ZeshuLiu/PolaMiya/结构Rev2/电路/机身主控/C_0603_1608Metric.SLDASM

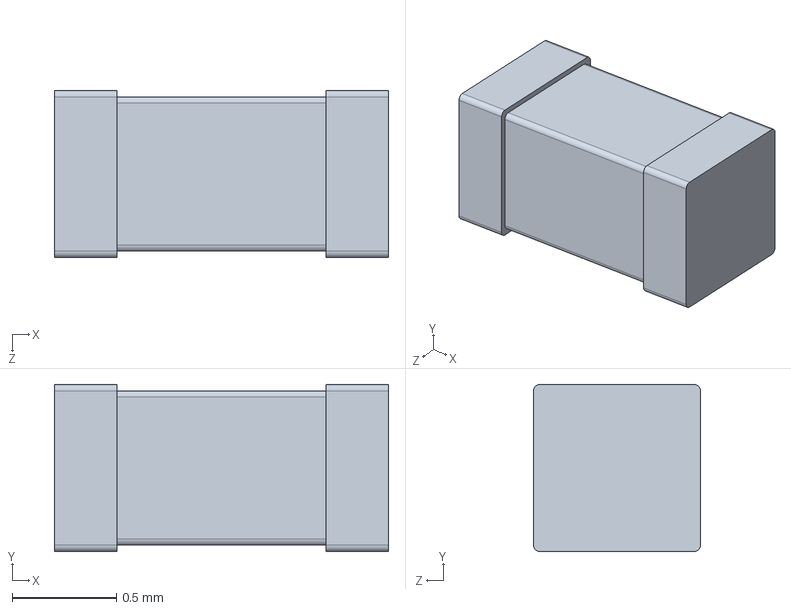
[picture p11: CAD file, 2025-02-23, last stored version]
结构Rev2/电路/机身主控/C_0603_1608Metric.SLDASM
1.60 x 0.8 x 0.8 mm
