ZeshuLiu/PolaMiya/电路/sdm18串口.SLDPRT

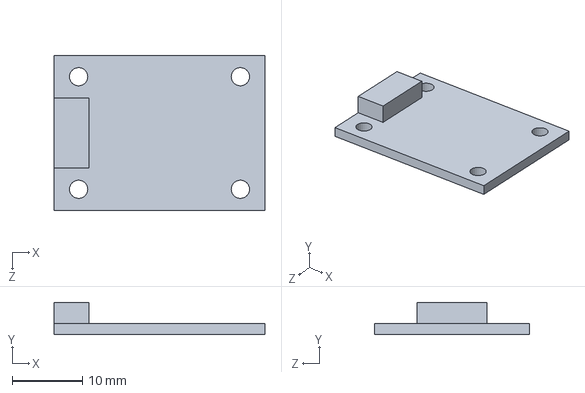
[picture p12: CAD file, 2025-06-10, last stored version]
电路/sdm18串口.SLDPRT
30.0 x 4.60 x 22.0 mm
