ZeshuLiu/PolaMiya/电路/主控器/DispKey/DispKeyR1_0.step

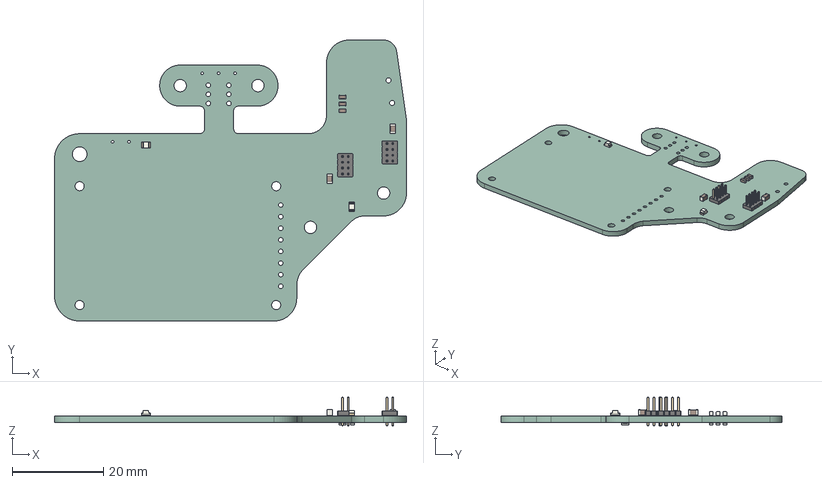
[picture p13: CAD file, 2025-06-10, last stored version]
电路/主控器/DispKey/DispKeyR1_0.step
77.0 x 61.5 x 6.30 mm
LED_0805_2012Metric x 2
C_0805_2012Metric x 2
C_0603_1608Metric x 3
PinHeader_2x04_P1.27mm_Vertical x 2
R_0603_1608Metric x 4
DispKey_PCB
