ZeshuLiu/PolaMiya/结构/原厂零件/吐片口机身钣金.SLDPRT

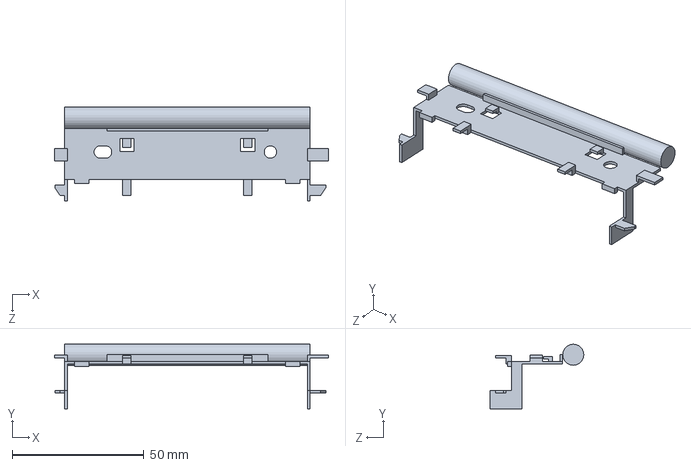
[picture p16: CAD file, 2025-02-23, last stored version]
结构/原厂零件/吐片口机身钣金.SLDPRT
103.8 x 24.5 x 35.5 mm
