ZeshuLiu/PolaMiya/结构/吐片机构/齿轮罩.SLDPRT

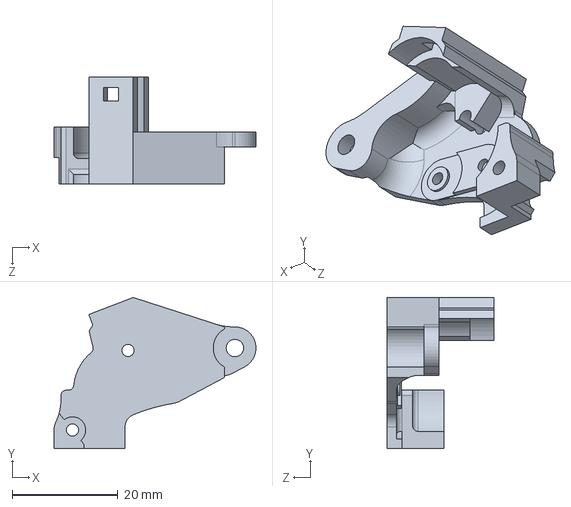
[picture p17: CAD file, 2025-07-19, last stored version]
结构/吐片机构/齿轮罩.SLDPRT
38.2 x 28.6 x 20.2 mm
