ZeshuLiu/PolaMiya/结构/外壳/STL/6吐片上巴.STL

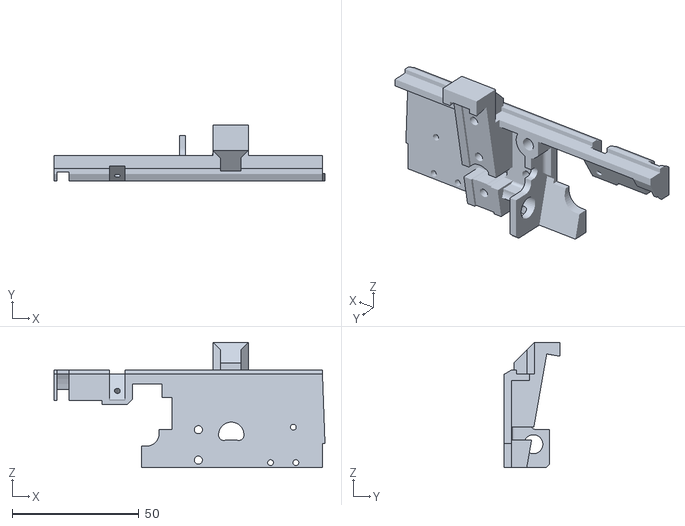
[picture p18: CAD file, 2025-02-23, last stored version]
结构/外壳/STL/6吐片上巴.STL
107.0 x 22.0 x 49.5
