ZeshuLiu/PolaMiya/结构/外壳/后挡板.SLDPRT

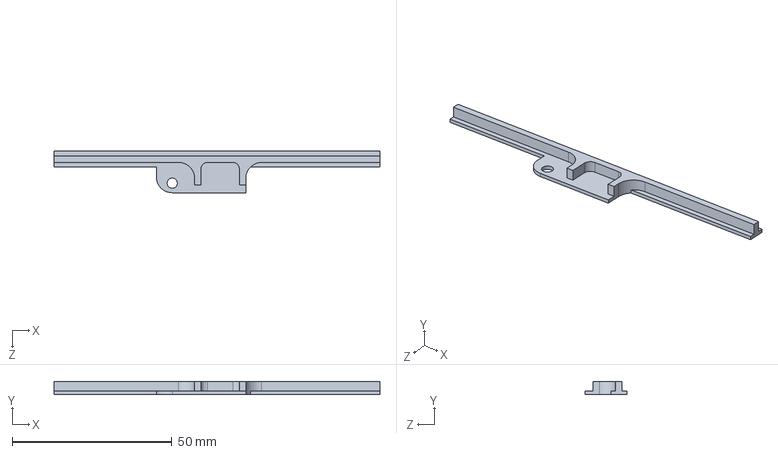
[picture p19: CAD file, 2025-09-27, last stored version]
结构/外壳/后挡板.SLDPRT
102.0 x 4.00 x 13.0 mm
