ZeshuLiu/PolaMiya/结构/片仓/STL/15左侧副支架.3mf

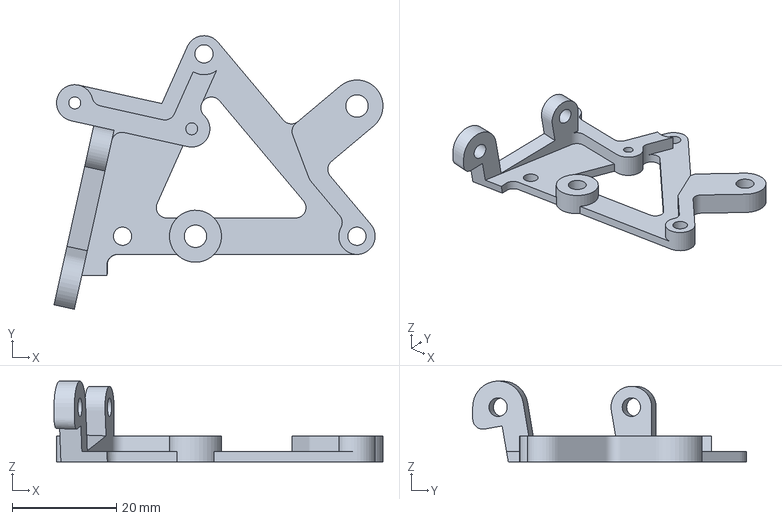
[picture p20: CAD file, 2025-06-10, last stored version]
结构/片仓/STL/15左侧副支架.3mf
63.2 x 52.5 x 15.5 mm
