ZeshuLiu/PolaMiya/结构/配件/STL/片仓消光绒.3mf

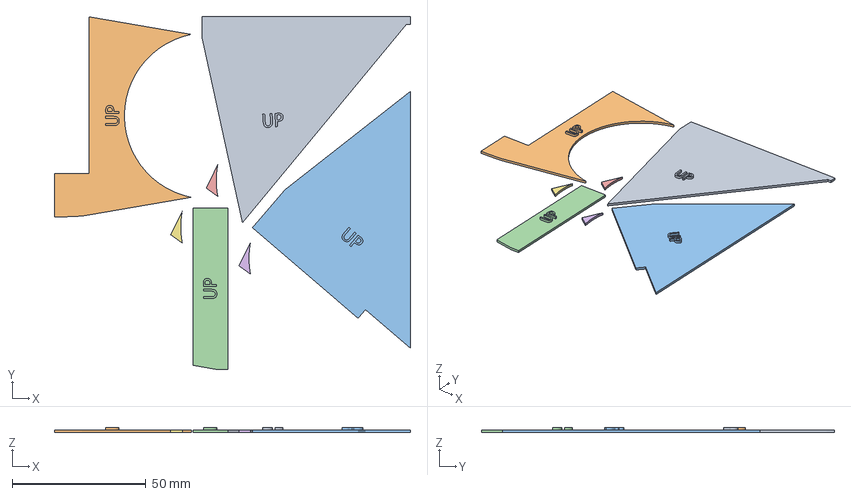
[picture p21: CAD file, 2025-09-27, last stored version]
结构/配件/STL/片仓消光绒.3mf
133.1 x 131.8 x 2.00 mm
片仓消光绒2.STL
片仓消光绒3.STL
片仓消光绒1.STL
片仓消光绒5.STL
片仓消光绒4.STL x 3
