ZeshuLiu/PolaMiya/结构/配件/片仓消光绒6.SLDPRT

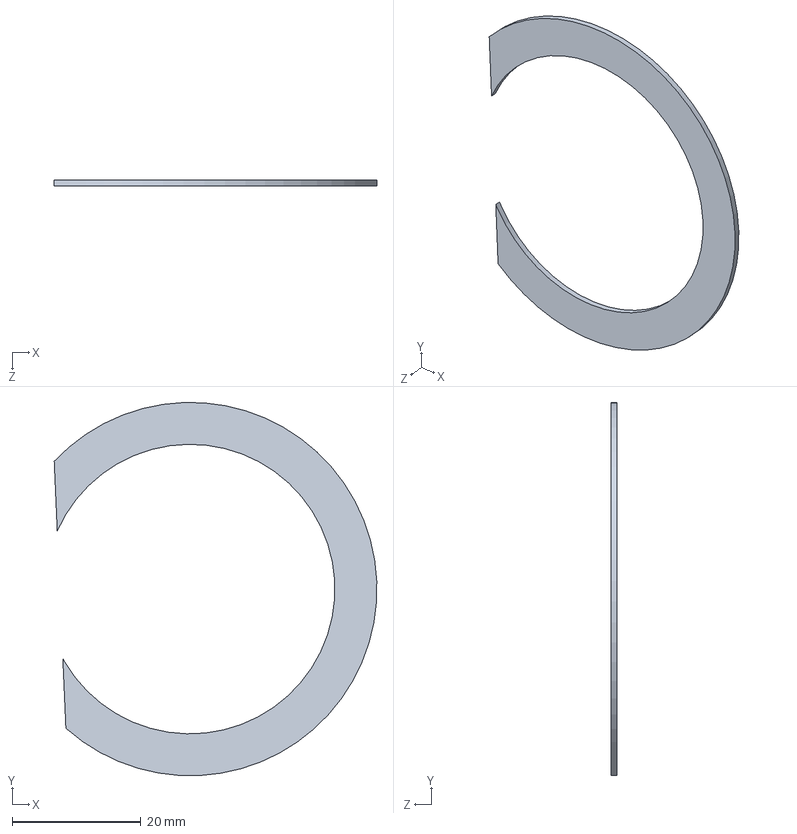
[picture p22: CAD file, 2025-09-27, last stored version]
结构/配件/片仓消光绒6.SLDPRT
50.1 x 58.0 x 1.00 mm
