ZeshuLiu/PolaMiya/结构Rev2/t/PolamiaPCB.step

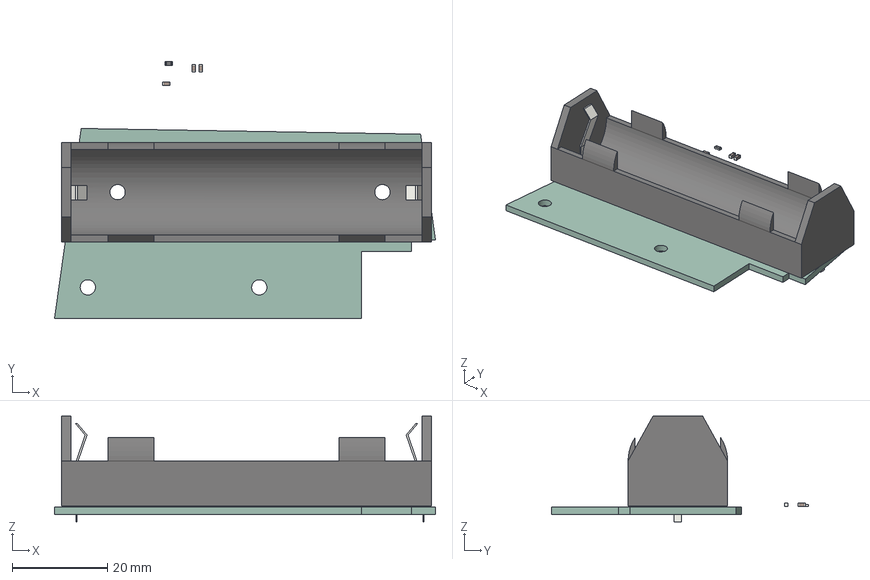
[picture p23: CAD file, 2025-02-23, last stored version]
结构Rev2/t/PolamiaPCB.step
80.0 x 53.9 x 22.2 mm
C_0603_1608Metric x 3
R_0603_1608Metric
MPD_BH_18650_PC2
PolamiaPCB_PCB
