ZeshuLiu/PolaMiya/结构Rev2/吐片机构/stps/吐片机构.STEP

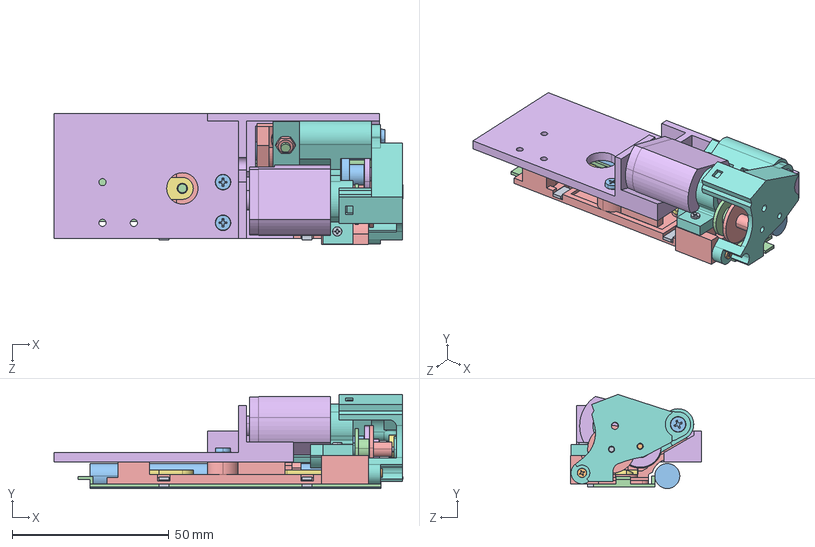
[picture p24: CAD file, 2025-02-23, last stored version]
结构Rev2/吐片机构/stps/吐片机构.STEP
111.5 x 30.1 x 42.0 mm
吐片口机身钣金
吐片钣金连接件
MG825
吐片钣金固定销 x 2
马达座
1.6x14.6
1.6x20.6
齿轮A
齿轮B
齿轮C
齿轮D
齿轮E
齿轮罩
cross recessed cheese head screws type a gb_GB_CROSS_SCREWS_TYPE135 M2X7-N
cross recessed cheese head screws type a gb_GB_CROSS_SCREWS_TYPE135 M2X6-N
cross recessed cheese head screws type a gb_GB_CROSS_SCREWS_TYPE135 M3X6-N x 3
cross recessed cheese head screws type a gb_GB_CROSS_SCREWS_TYPE135 M3X8-N
hex thin nuts-grades ab-chamfered gb_GB_FASTENER_NUT_STNAB M3-N
吐片上巴
