ZeshuLiu/PolaMiya/结构Rev2/测试用/法兰距测试/对焦框10080.SLDPRT

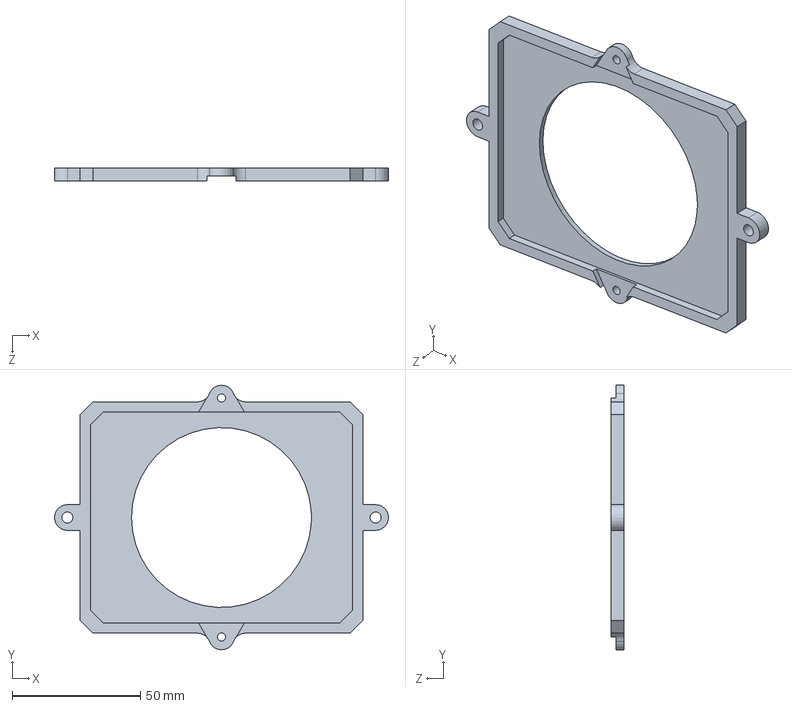
[picture p25: CAD file, 2025-02-23, last stored version]
结构Rev2/测试用/法兰距测试/对焦框10080.SLDPRT
130.0 x 103.0 x 5.00 mm
