ZeshuLiu/PolaMiya/结构Rev2/片仓吐片总成/STL/片仓吐片一体STL.3mf

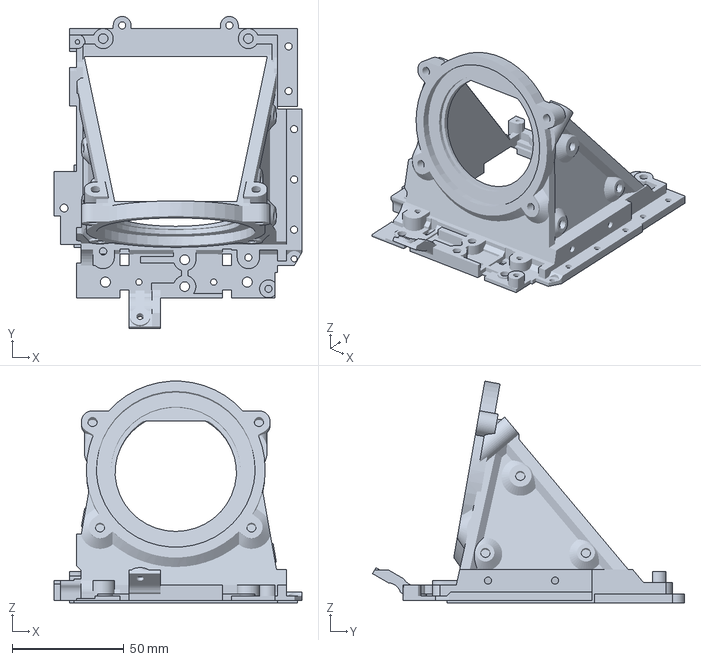
[picture p26: CAD file, 2025-09-27, last stored version]
结构Rev2/片仓吐片总成/STL/片仓吐片一体STL.3mf
111.0 x 139.6 x 99.3 mm
