ZeshuLiu/PolaMiya/结构Rev2/片仓吐片总成/吐片上巴.SLDPRT

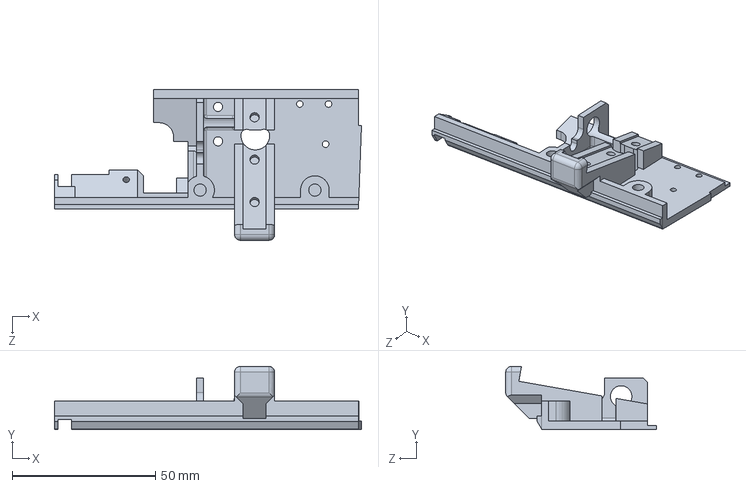
[picture p27: CAD file, 2025-09-27, last stored version]
结构Rev2/片仓吐片总成/吐片上巴.SLDPRT
107.0 x 22.0 x 52.5 mm
