ZeshuLiu/PolaMiya/结构Rev2/电路/DispKey_R1_0/DispKey_PCB.SLDPRT

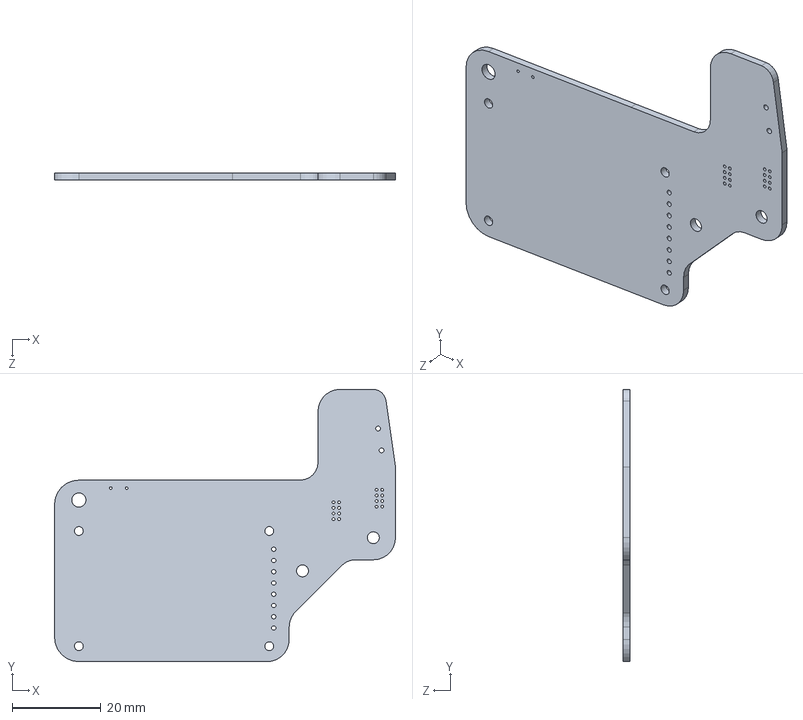
[picture p28: CAD file, 2025-06-10, last stored version]
结构Rev2/电路/DispKey_R1_0/DispKey_PCB.SLDPRT
77.0 x 61.5 x 1.51 mm
