ZeshuLiu/PolaMiya/结构Rev2/电路/电池按钮.SLDPRT

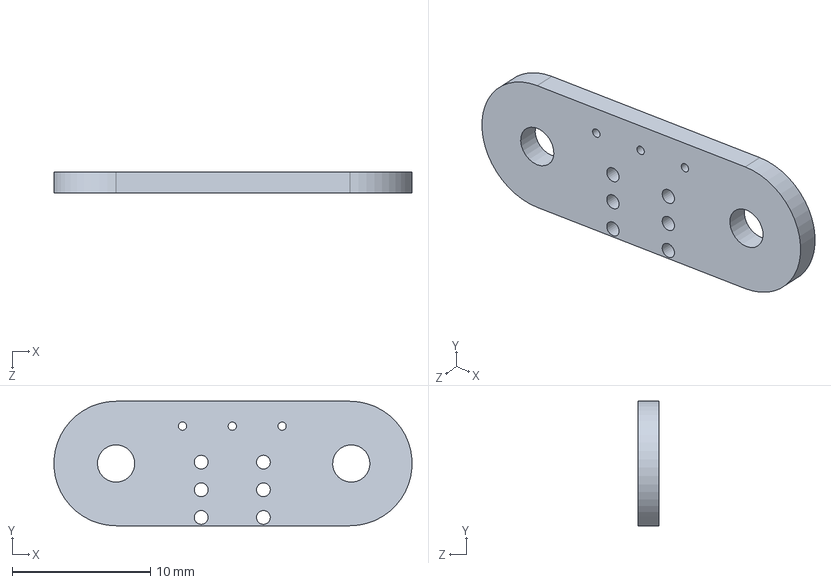
[picture p29: CAD file, 2025-06-10, last stored version]
结构Rev2/电路/电池按钮.SLDPRT
25.9 x 9.00 x 1.51 mm
