ZeshuLiu/PolaMiya/结构Rev2/配件/Mamiya127镜头盖后盖.SLDPRT

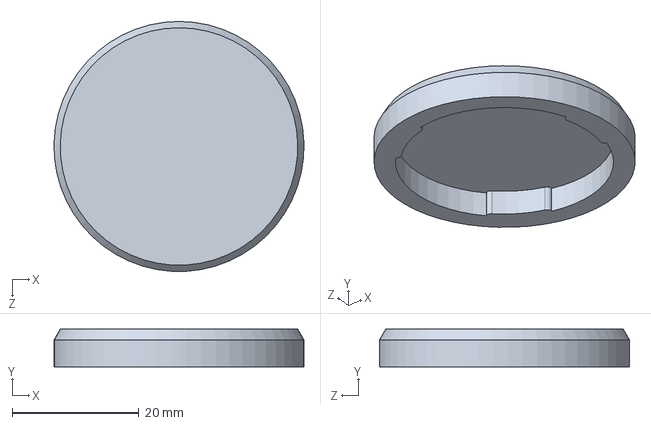
[picture p30: CAD file, 2025-02-23, last stored version]
结构Rev2/配件/Mamiya127镜头盖后盖.SLDPRT
39.5 x 6.00 x 39.5 mm
