ZeshuLiu/PolaMiya/结构Rev2/配件/STL/55mm_Spring.stl

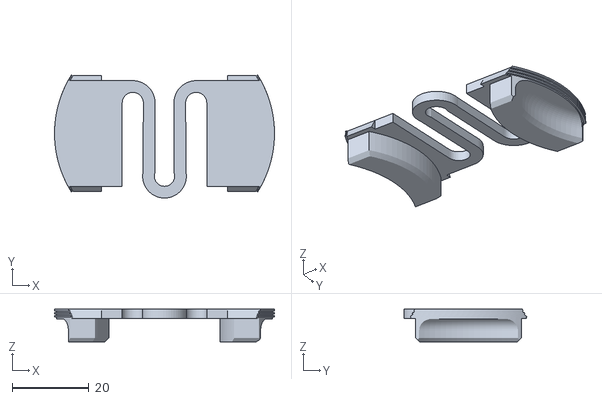
[picture p31: CAD file, 2025-02-23, last stored version]
结构Rev2/配件/STL/55mm_Spring.stl
57.2 x 32.0 x 8.50
