ZeshuLiu/PolaMiya/结构Rev2/采购零件/大头拨轮.SLDPRT

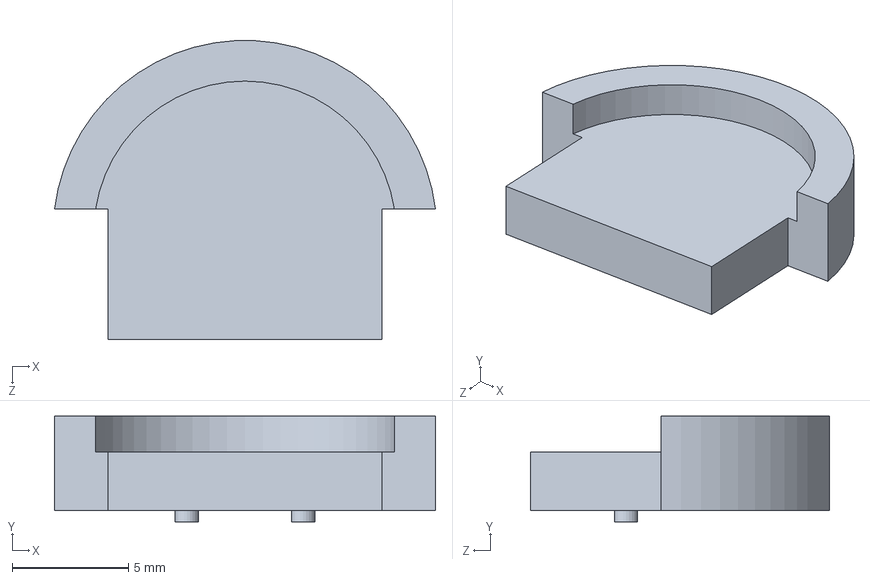
[picture p32: CAD file, 2025-06-29, last stored version]
结构Rev2/采购零件/大头拨轮.SLDPRT
16.4 x 4.55 x 12.8 mm
