ZeshuLiu/PolaMiya/结构Rev2/镜头总成/STL/1调焦桶盖+4内环.3mf

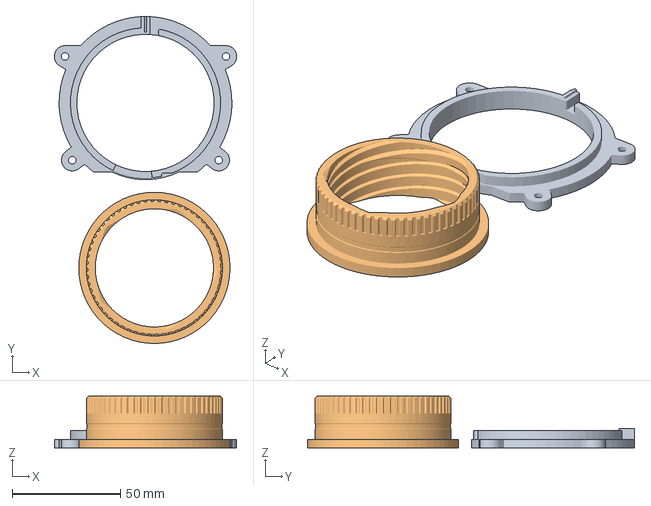
[picture p33: CAD file, 2025-02-23, last stored version]
结构Rev2/镜头总成/STL/1调焦桶盖+4内环.3mf
84.5 x 151.3 x 24.0 mm
1调焦桶盖.STL
4内环.STL
