ZeshuLiu/PolaMiya/结构Rev2N/全息取景器/标靶.SLDPRT

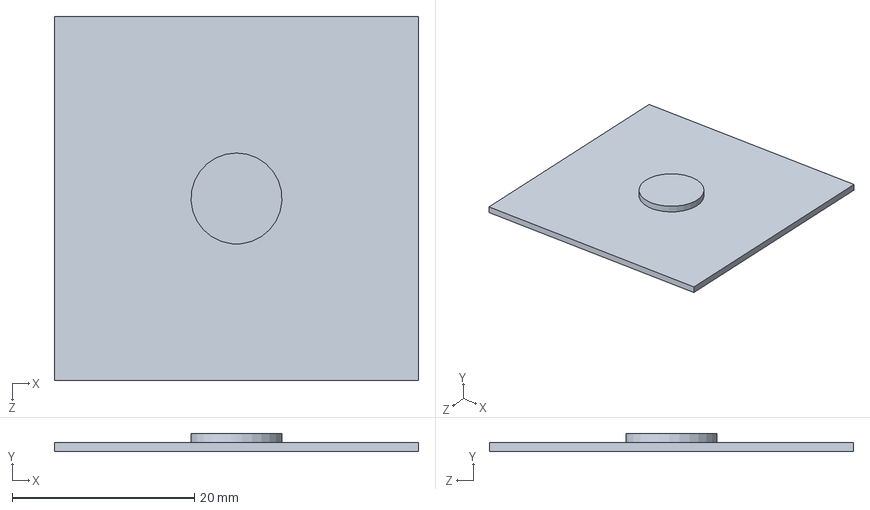
[picture p34: CAD file, 2026-03-20, last stored version]
结构Rev2N/全息取景器/标靶.SLDPRT
40.0 x 2.00 x 40.0 mm
