ZeshuLiu/PolaMiya/结构Rev2N/吐片机构/STLs/钣金突起衬垫.3mf

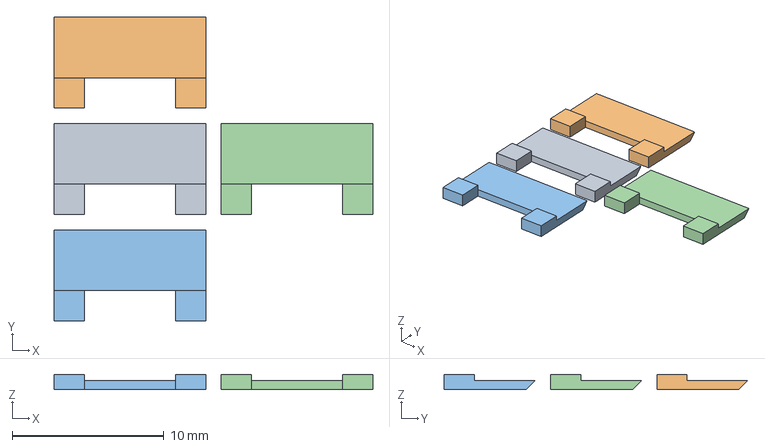
[picture p35: CAD file, 2026-02-14, last stored version]
结构Rev2N/吐片机构/STLs/钣金突起衬垫.3mf
21.0 x 20.0 x 1.00 mm
钣金突起衬垫.STL x 4
