ZeshuLiu/PolaMiya/结构Rev2N/吐片机构/stps/马达座.STEP

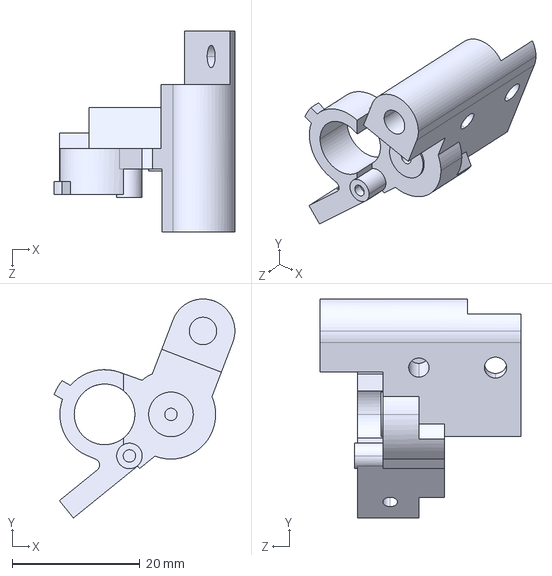
[picture p36: CAD file, 2025-02-23, last stored version]
结构Rev2N/吐片机构/stps/马达座.STEP
28.3 x 34.3 x 31.5 mm
