ZeshuLiu/PolaMiya/结构Rev2N/吐片机构/齿轮定位.SLDPRT

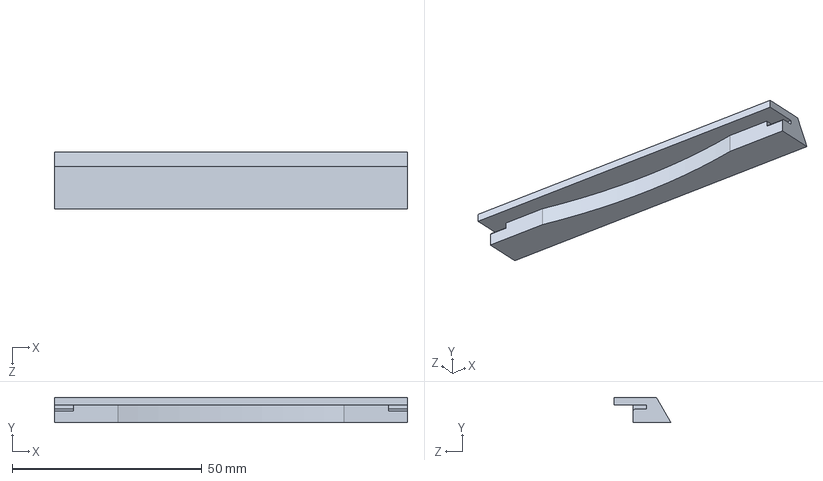
[picture p37: CAD file, 2026-02-14, last stored version]
结构Rev2N/吐片机构/齿轮定位.SLDPRT
93.1 x 6.60 x 15.0 mm
