ZeshuLiu/PolaMiya/结构Rev2N/外壳/STL/闪光灯线.3mf

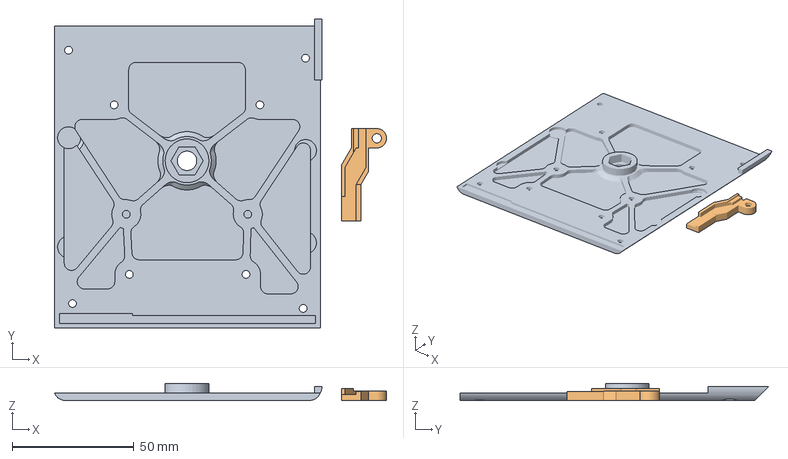
[picture p38: CAD file, 2025-09-27, last stored version]
结构Rev2N/外壳/STL/闪光灯线.3mf
136.6 x 127.0 x 7.00 mm
底壳.STL
闪光灯线.STL
