ZeshuLiu/PolaMiya/结构Rev2N/消光绒模板/STL/消光绒.3mf

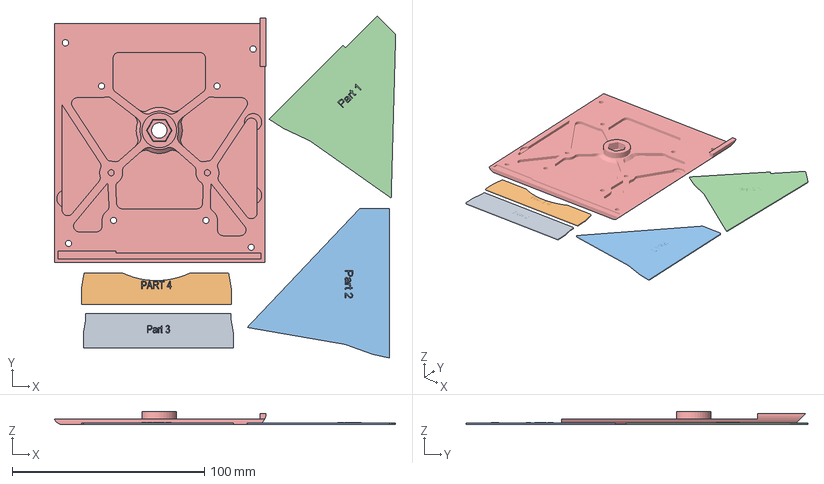
[picture p40: CAD file, 2025-09-27, last stored version]
结构Rev2N/消光绒模板/STL/消光绒.3mf
177.4 x 177.7 x 7.00 mm
后侧.STL
前侧.STL
右内壁.STL
左内壁.STL
底壳.STL
