ZeshuLiu/PolaMiya/结构Rev2N/消光绒模板/前侧.SLDPRT

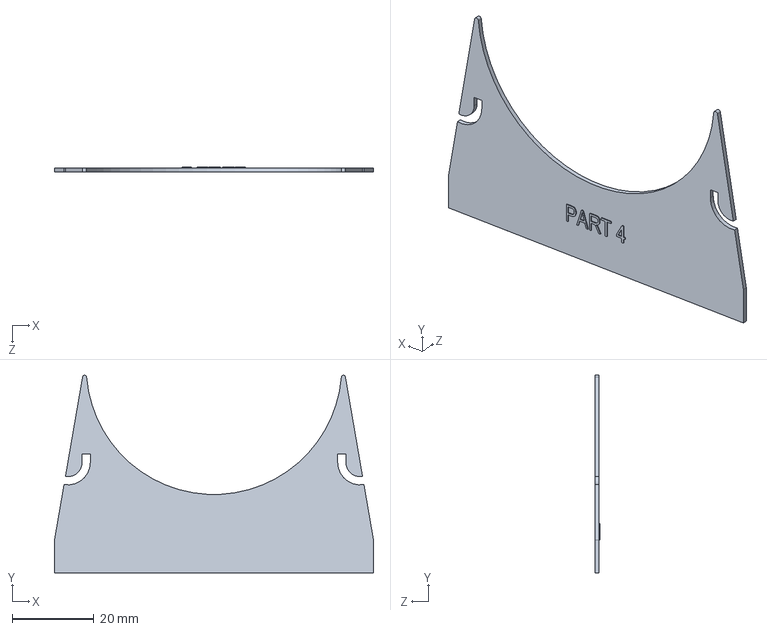
[picture p41: CAD file, 2026-03-20, last stored version]
结构Rev2N/消光绒模板/前侧.SLDPRT
78.0 x 48.3 x 1.20 mm
