ZeshuLiu/PolaMiya/结构Rev2N/片仓总成/STL/主片仓测试2.3mf

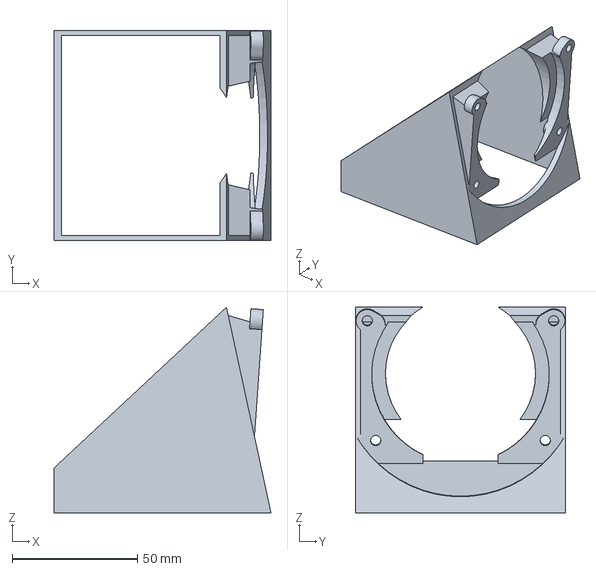
[picture p42: CAD file, 2025-09-27, last stored version]
结构Rev2N/片仓总成/STL/主片仓测试2.3mf
86.7 x 84.0 x 82.2 mm
