ZeshuLiu/PolaMiya/结构Rev2N/片仓总成/STP/右侧板.STEP

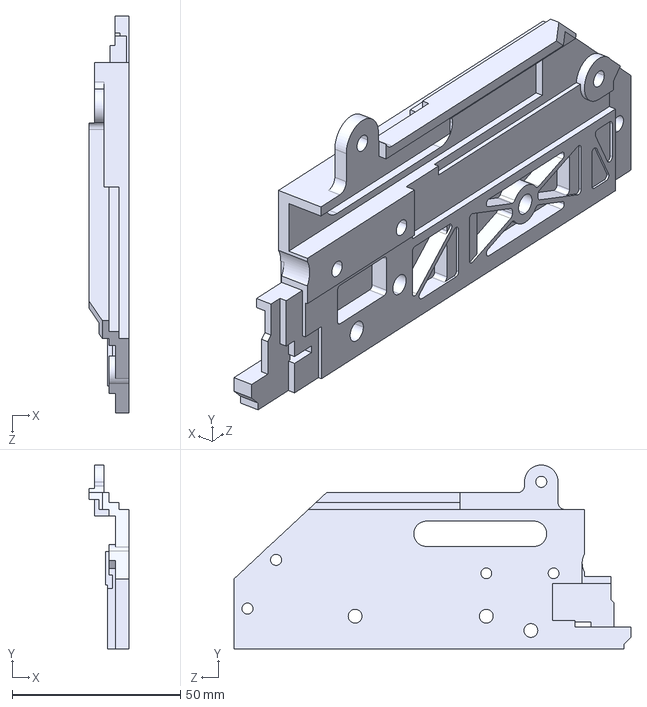
[picture p43: CAD file, 2026-03-20, last stored version]
结构Rev2N/片仓总成/STP/右侧板.STEP
12.0 x 54.7 x 118.0 mm
