ZeshuLiu/PolaMiya/结构Rev2N/电路/闪光灯.SLDPRT

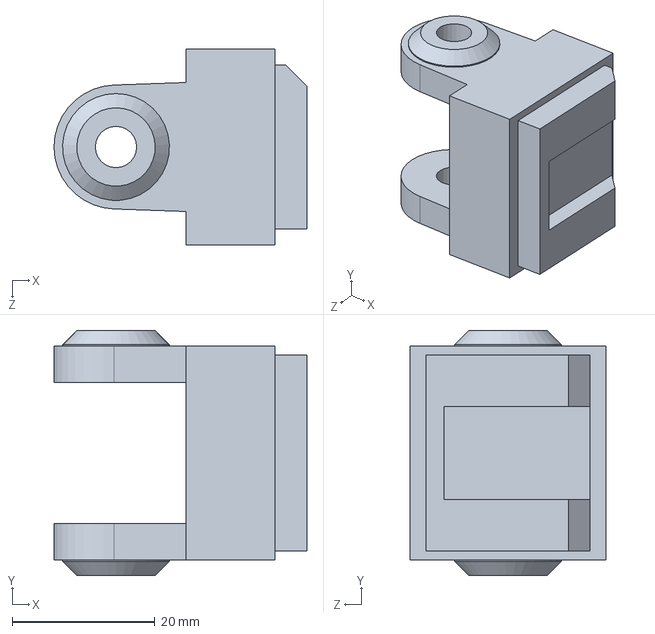
[picture p46: CAD file, 2025-12-25, last stored version]
结构Rev2N/电路/闪光灯.SLDPRT
35.5 x 34.4 x 27.5 mm
