ZeshuLiu/PolaMiya/结构Rev2N/零散打印stl/齿轮定位.3mf

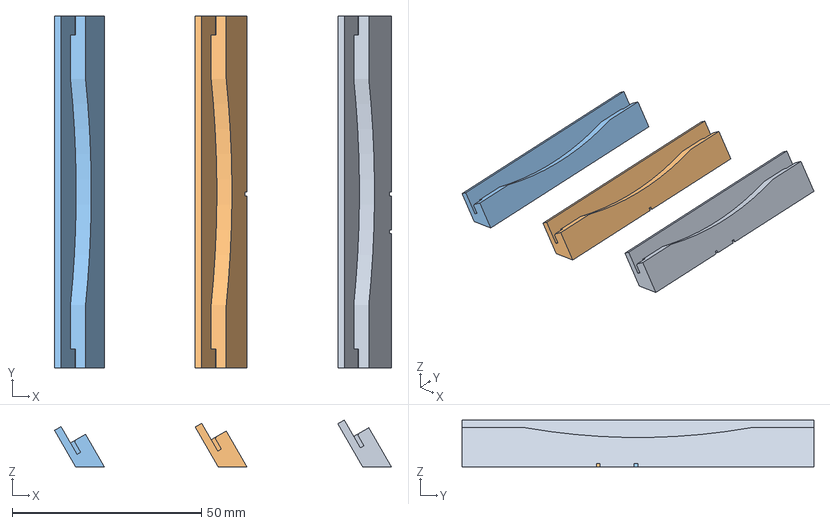
[picture p48: CAD file, 2026-03-20, last stored version]
结构Rev2N/零散打印stl/齿轮定位.3mf
89.1 x 93.1 x 12.4 mm
齿轮定位+2mm.STL
齿轮定位+1mm.STL
齿轮定位.STL
