ZeshuLiu/PolaMiya/电路/闪光灯转接/FlashAdapter/FlashAdapter.step

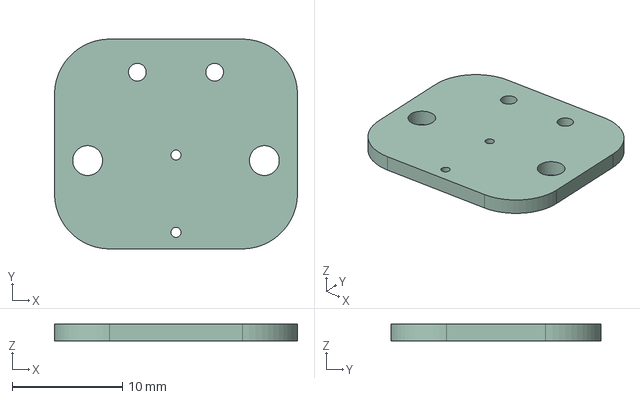
[picture p49: CAD file, 2025-11-23, last stored version]
电路/闪光灯转接/FlashAdapter/FlashAdapter.step
22.0 x 19.0 x 1.51 mm
