ZeshuLiu/PolaMiya/结构/吐片机构/反光镜筒2.SLDPRT

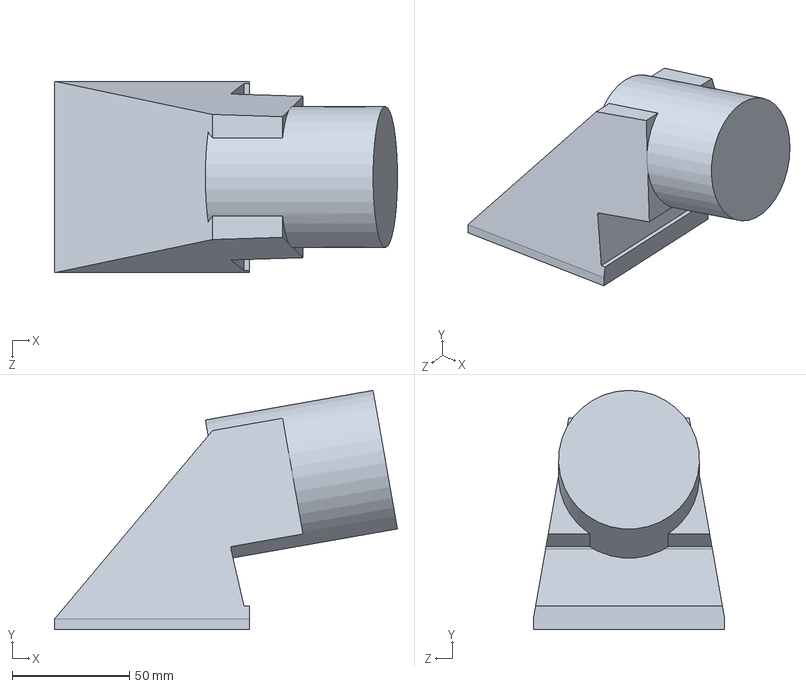
[picture p50: CAD file, 2025-02-23, last stored version]
结构/吐片机构/反光镜筒2.SLDPRT
146.0 x 101.9 x 81.5 mm
