ZeshuLiu/PolaMiya/结构/外壳/右上巴壳.SLDPRT

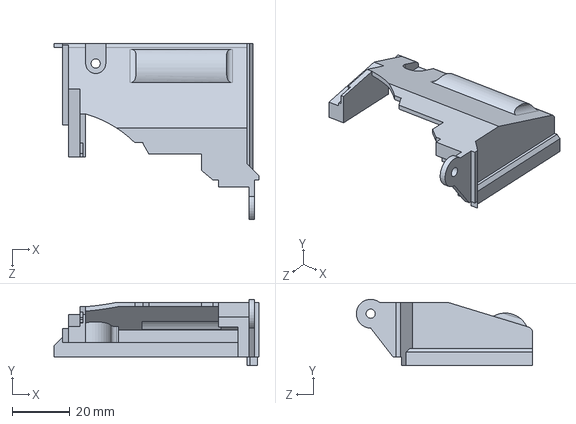
[picture p51: CAD file, 2025-09-27, last stored version]
结构/外壳/右上巴壳.SLDPRT
71.2 x 23.1 x 61.3 mm
