ZeshuLiu/PolaMiya/结构/片仓/STL/11片盒弹簧.STL

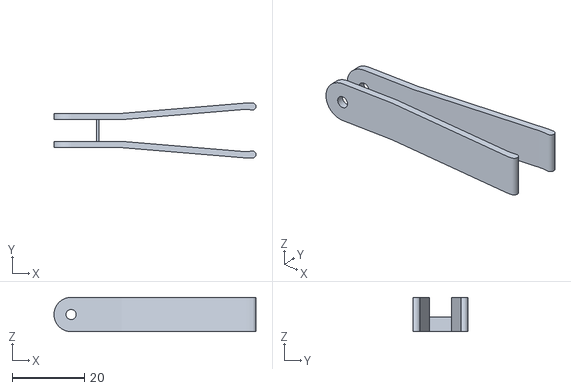
[picture p52: CAD file, 2025-06-10, last stored version]
结构/片仓/STL/11片盒弹簧.STL
56.0 x 15.4 x 9.50
