ZeshuLiu/PolaMiya/结构/片仓/片仓中框.SLDPRT

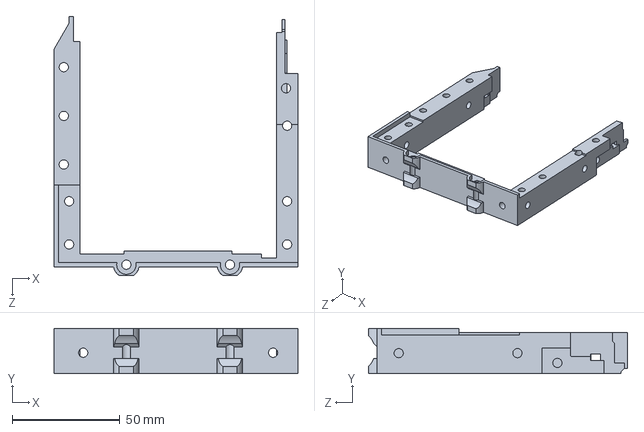
[picture p53: CAD file, 2025-09-27, last stored version]
结构/片仓/片仓中框.SLDPRT
113.0 x 21.0 x 120.0 mm
