ZeshuLiu/PolaMiya/结构/配件/消光棉6.DXF

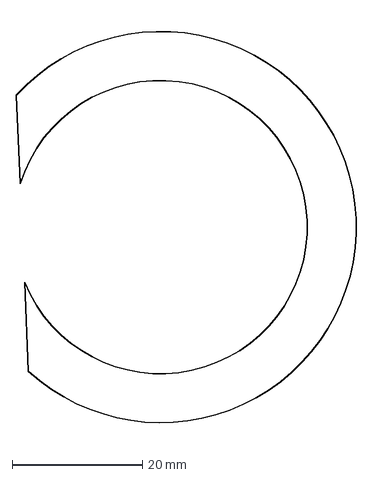
[picture p54: CAD file, 2025-09-27, last stored version]
结构/配件/消光棉6.DXF
52.7 x 64.7 mm
