ZeshuLiu/PolaMiya/结构/镜头总成/MamiyaPressLensSeat.SLDPRT

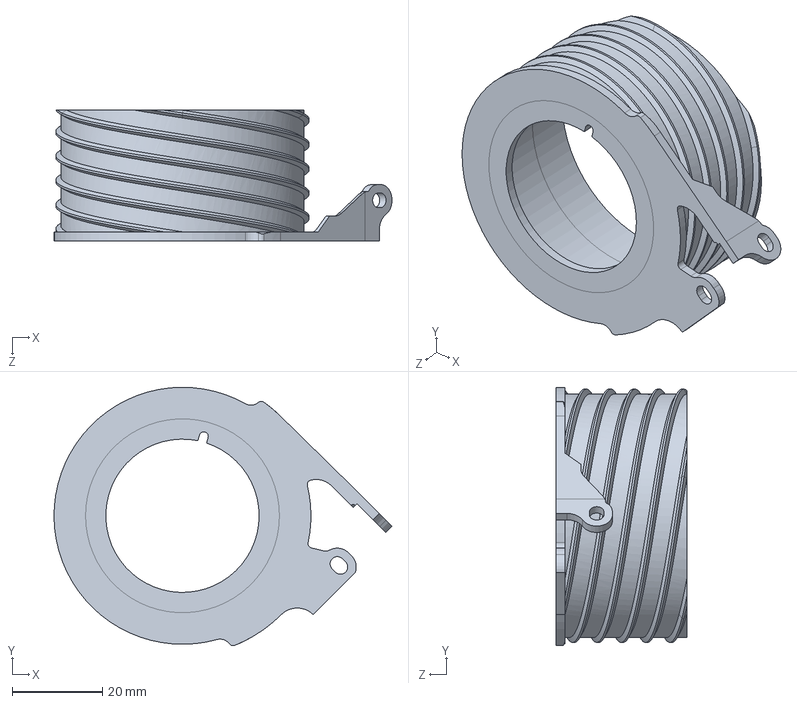
[picture p55: CAD file, 2025-02-23, last stored version]
结构/镜头总成/MamiyaPressLensSeat.SLDPRT
75.0 x 57.3 x 29.0 mm
