ZeshuLiu/PolaMiya/结构Rev2/吐片机构/吐片钣金固定销.SLDPRT

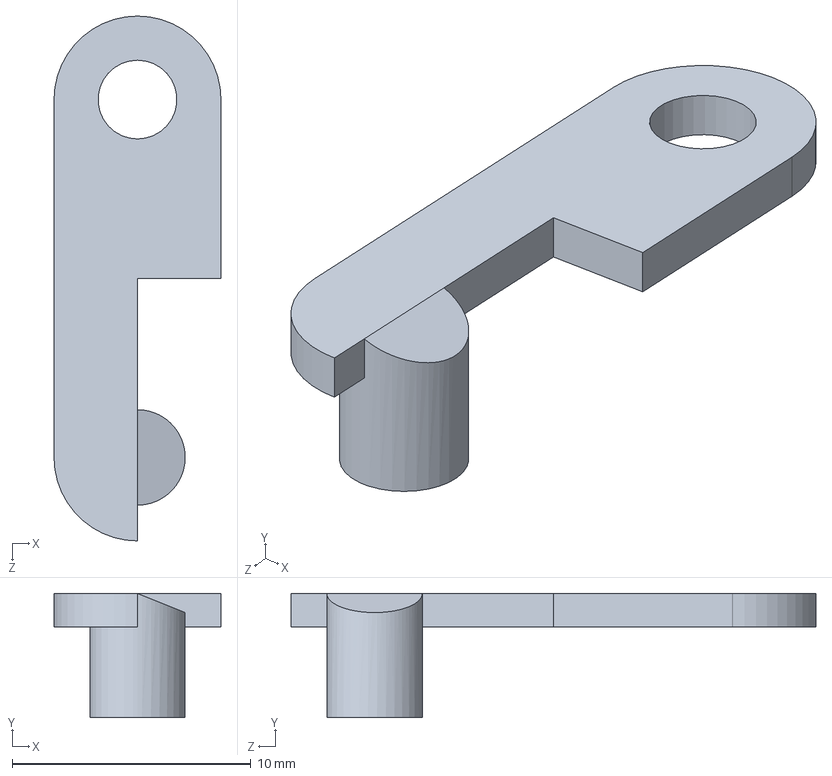
[picture p56: CAD file, 2025-02-23, last stored version]
结构Rev2/吐片机构/吐片钣金固定销.SLDPRT
7.00 x 5.20 x 22.0 mm
