ZeshuLiu/PolaMiya/结构Rev2/外壳/背下壳.SLDPRT

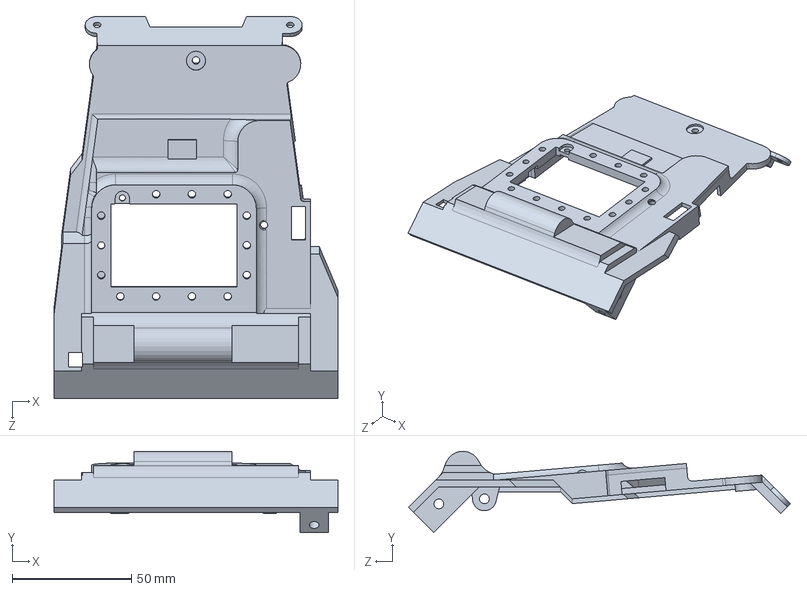
[picture p57: CAD file, 2025-07-19, last stored version]
结构Rev2/外壳/背下壳.SLDPRT
119.0 x 34.0 x 160.1 mm
