ZeshuLiu/PolaMiya/结构Rev2/片仓/STL/5片仓中框.3mf

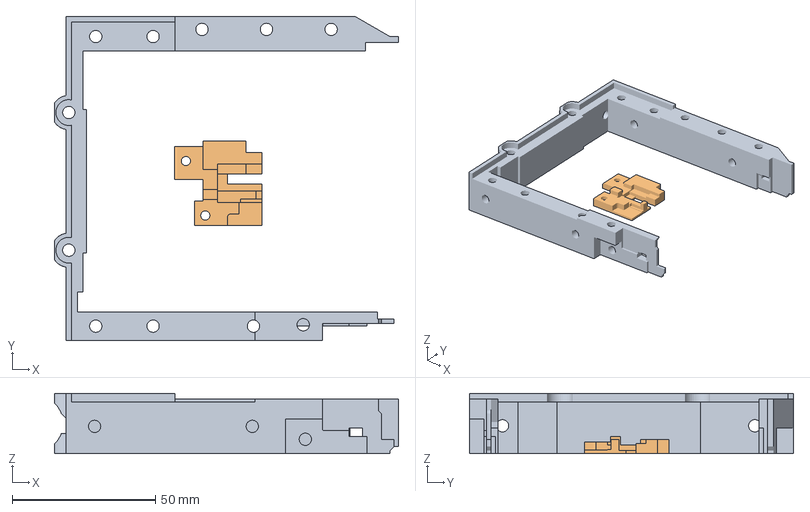
[picture p58: CAD file, 2025-06-10, last stored version]
结构Rev2/片仓/STL/5片仓中框.3mf
120.0 x 113.0 x 21.0 mm
5片仓中框.STL
14推杆外框.STL
