ZeshuLiu/PolaMiya/结构Rev2/片仓/片仓地板.SLDPRT

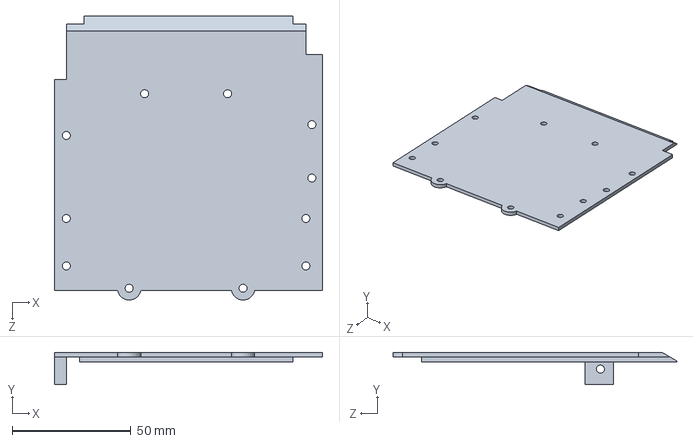
[picture p59: CAD file, 2025-06-29, last stored version]
结构Rev2/片仓/片仓地板.SLDPRT
113.0 x 13.5 x 119.7 mm
