ZeshuLiu/PolaMiya/结构Rev2/电路/电池正极弹片.SLDPRT

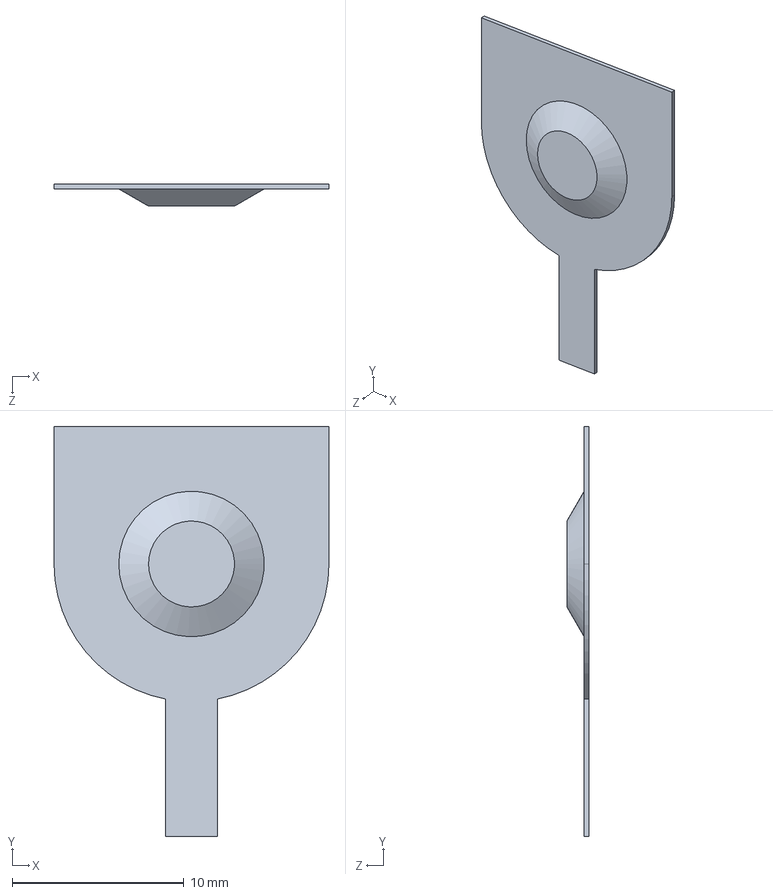
[picture p60: CAD file, 2025-06-10, last stored version]
结构Rev2/电路/电池正极弹片.SLDPRT
16.0 x 23.9 x 1.30 mm
