ZeshuLiu/PolaMiya/结构Rev2/配件/Mamiya127铭牌.SLDPRT

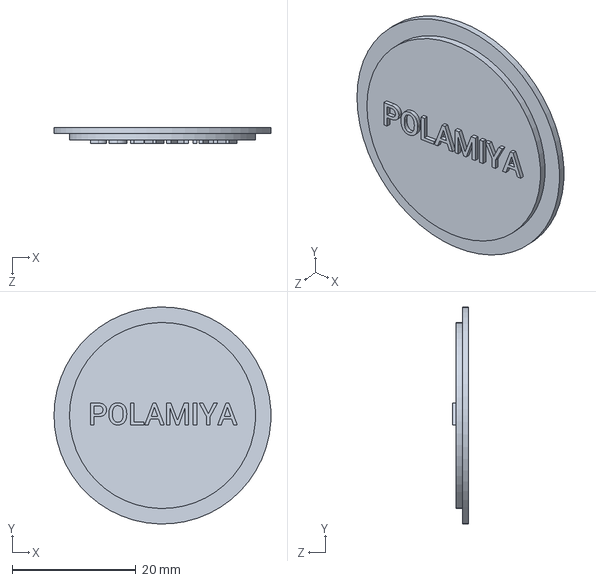
[picture p61: CAD file, 2025-02-23, last stored version]
结构Rev2/配件/Mamiya127铭牌.SLDPRT
35.0 x 35.0 x 2.60 mm
