ZeshuLiu/PolaMiya/结构Rev2/配件/STL/55mm_Thingverse.3mf

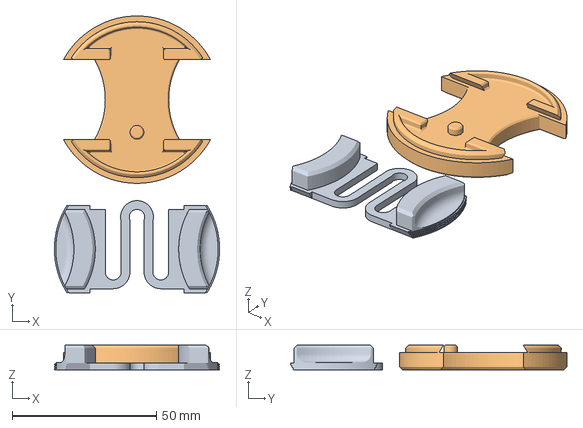
[picture p62: CAD file, 2025-02-23, last stored version]
结构Rev2/配件/STL/55mm_Thingverse.3mf
57.2 x 96.0 x 8.50 mm
55mm_Spring.stl
55mm_Body.stl
