ZeshuLiu/PolaMiya/结构Rev2/采购零件/SMT螺母M2.5H3.5.SLDPRT

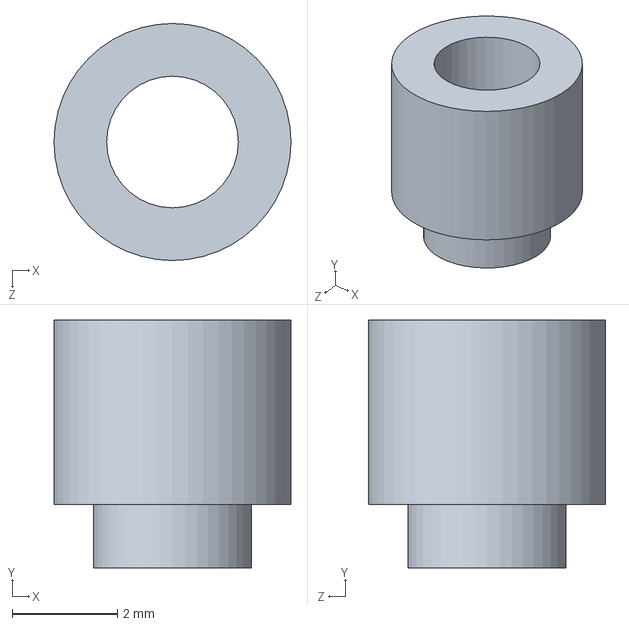
[picture p63: CAD file, 2025-06-29, last stored version]
结构Rev2/采购零件/SMT螺母M2.5H3.5.SLDPRT
4.50 x 4.70 x 4.50 mm
