ZeshuLiu/PolaMiya/结构Rev2/镜头总成/STL/2MamiyaPressLensSeat.3mf

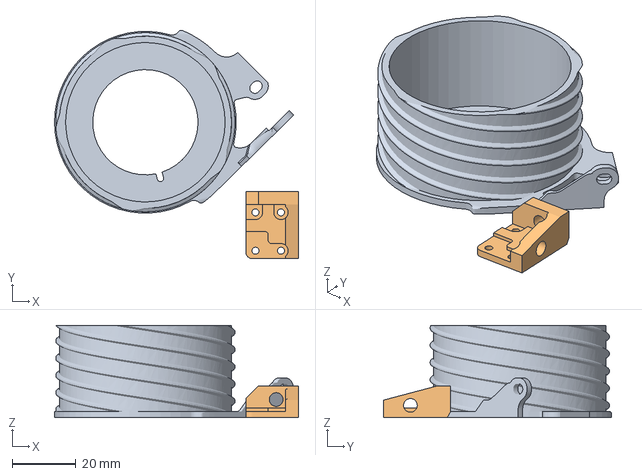
[picture p64: CAD file, 2025-02-23, last stored version]
结构Rev2/镜头总成/STL/2MamiyaPressLensSeat.3mf
76.5 x 71.6 x 29.0 mm
2MamiyaPressLensSeat.STL
3SliderConnect.STL
