ZeshuLiu/PolaMiya/结构Rev2N/全息取景器/镜座.SLDPRT

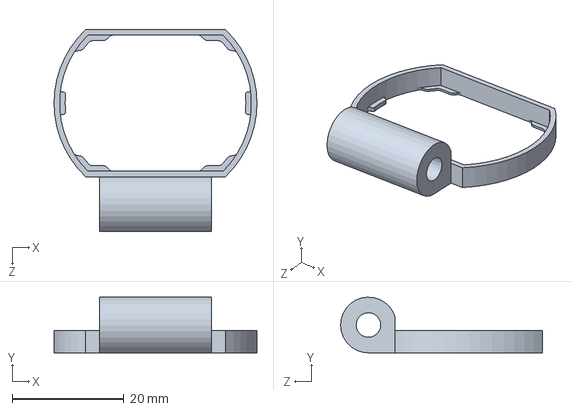
[picture p65: CAD file, 2026-03-20, last stored version]
结构Rev2N/全息取景器/镜座.SLDPRT
36.4 x 10.00 x 36.2 mm
