ZeshuLiu/PolaMiya/结构Rev2N/吐片机构/STLs/钣金衬垫.3mf

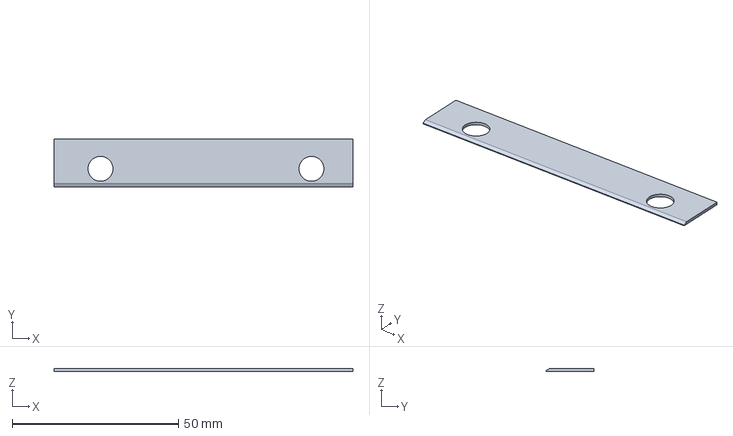
[picture p66: CAD file, 2026-02-14, last stored version]
结构Rev2N/吐片机构/STLs/钣金衬垫.3mf
90.0 x 14.5 x 0.8 mm
