ZeshuLiu/PolaMiya/结构Rev2N/吐片机构/取片盒工具.SLDPRT

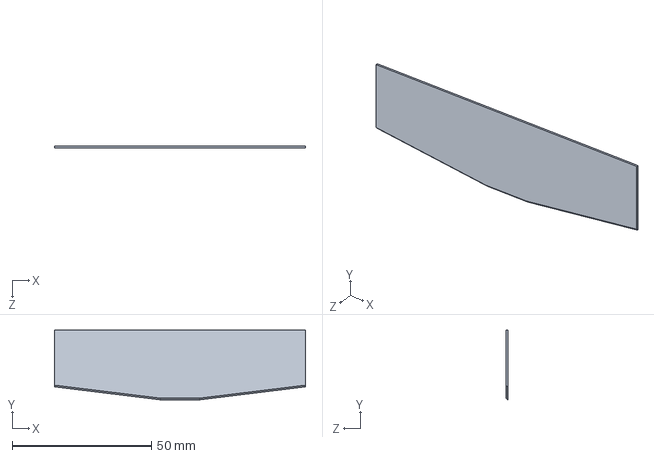
[picture p67: CAD file, 2026-02-14, last stored version]
结构Rev2N/吐片机构/取片盒工具.SLDPRT
90.0 x 25.0 x 0.6 mm
