ZeshuLiu/PolaMiya/结构Rev2N/外壳/左侧壳.SLDPRT

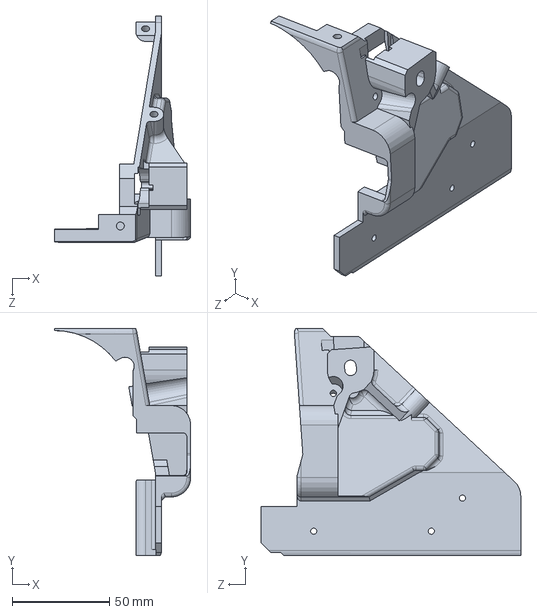
[picture p68: CAD file, 2026-03-20, last stored version]
结构Rev2N/外壳/左侧壳.SLDPRT
70.2 x 116.7 x 133.5 mm
