ZeshuLiu/PolaMiya/结构Rev2N/消光绒模板/镜筒.SLDPRT

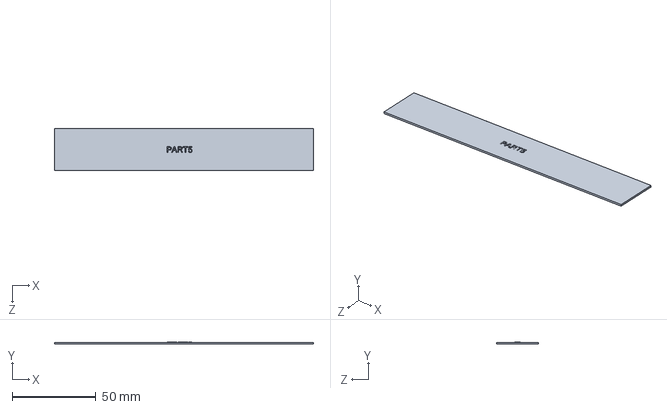
[picture p69: CAD file, 2026-03-20, last stored version]
结构Rev2N/消光绒模板/镜筒.SLDPRT
155.0 x 1.20 x 25.0 mm
