ZeshuLiu/PolaMiya/结构Rev2N/片仓总成/STL/内环L22.STL

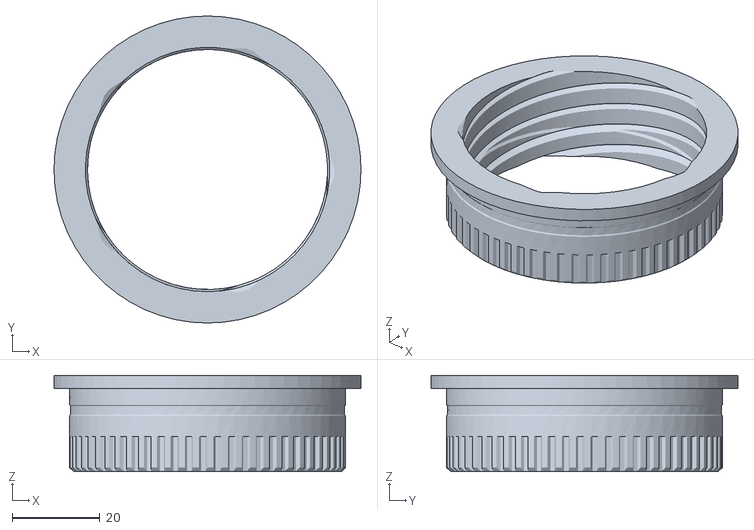
[picture p70: CAD file, 2025-09-27, last stored version]
结构Rev2N/片仓总成/STL/内环L22.STL
70.0 x 70.0 x 22.0
