ZeshuLiu/PolaMiya/结构Rev2N/片仓总成/齿轮定位.SLDPRT

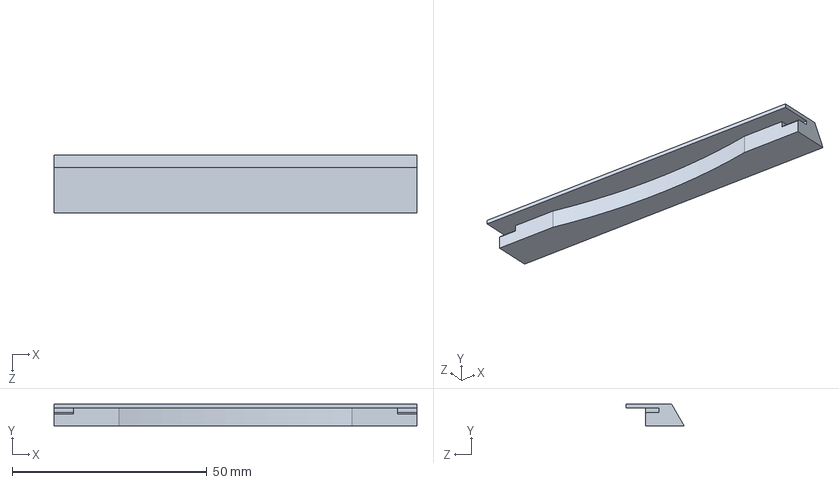
[picture p72: CAD file, 2026-03-20, last stored version]
结构Rev2N/片仓总成/齿轮定位.SLDPRT
93.1 x 5.60 x 15.0 mm
