ZeshuLiu/PolaMiya/结构Rev2N/电路/激光测距SDM18.SLDPRT

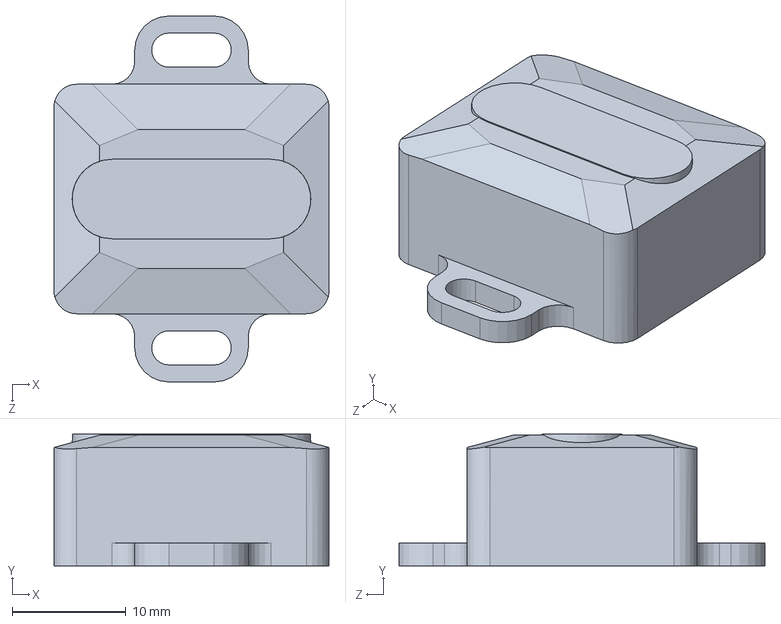
[picture p73: CAD file, 2025-09-27, last stored version]
结构Rev2N/电路/激光测距SDM18.SLDPRT
24.2 x 11.6 x 32.2 mm
