ZeshuLiu/PolaMiya/结构/片仓/STL/14推杆外框.STL

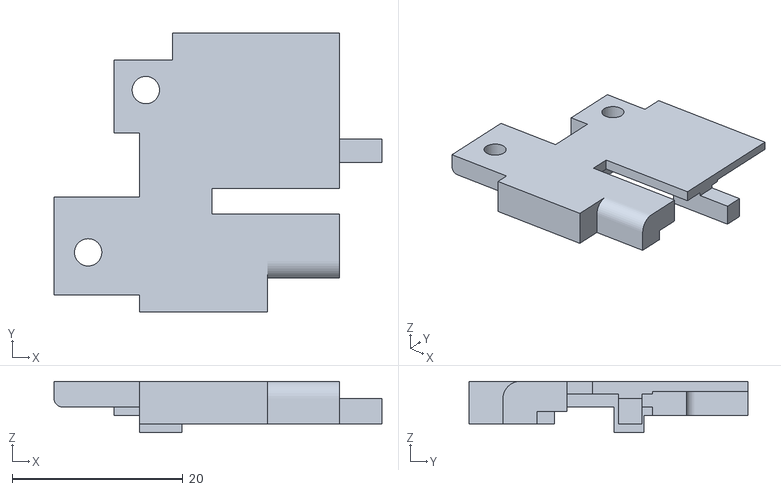
[picture p76: CAD file, 2025-06-10, last stored version]
结构/片仓/STL/14推杆外框.STL
38.4 x 32.7 x 6.00
