ZeshuLiu/PolaMiya/结构/片仓/片仓主框.SLDPRT

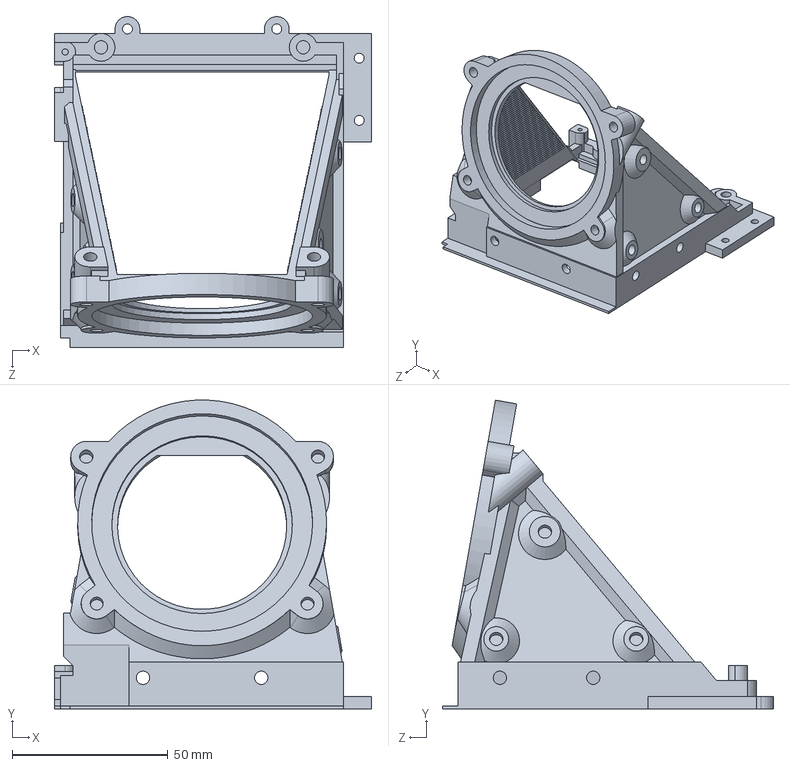
[picture p77: CAD file, 2025-09-27, last stored version]
结构/片仓/片仓主框.SLDPRT
102.0 x 99.3 x 106.4 mm
