ZeshuLiu/PolaMiya/结构/配件/STL/55mm_Body.stl

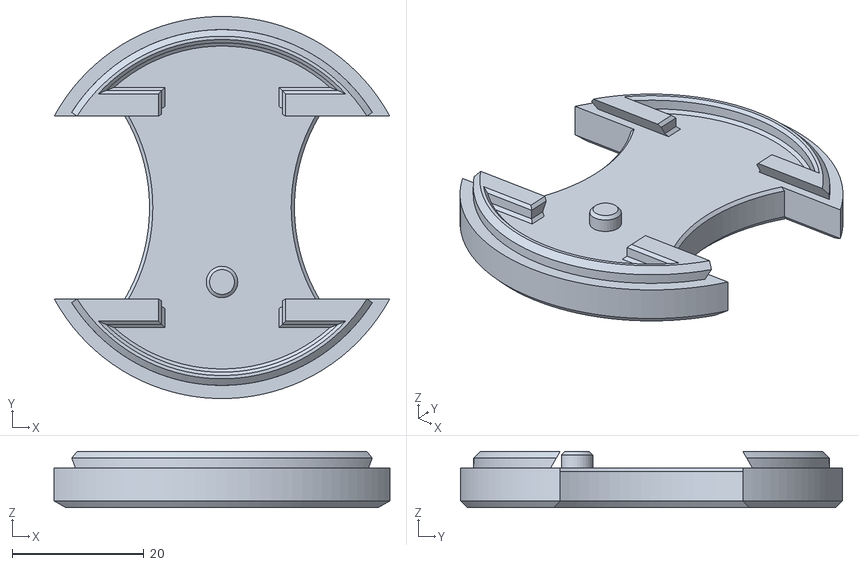
[picture p78: CAD file, 2025-02-23, last stored version]
结构/配件/STL/55mm_Body.stl
51.0 x 58.0 x 8.50
