ZeshuLiu/PolaMiya/结构Rev2/电路/DispKey_R1_0/DispKey_Screen_R1_0.SLDASM

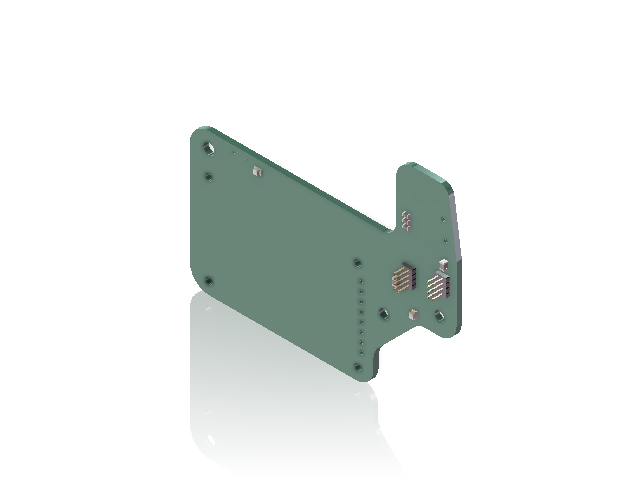
[picture p89: CAD file, 2025-06-10, last stored version]
结构Rev2/电路/DispKey_R1_0/DispKey_Screen_R1_0.SLDASM
LED_0805_2012Metric x 2
C_0805_2012Metric x 2
C_0603_1608Metric x 3
PinHeader_2x04_P1.27mm_Vertical x 2
R_0603_1608Metric x 4
DispKey_PCB
