ZeshuLiu/PolaMiya/结构/吐片机构/吐片机构_LAPTOP-NACPAVO6_7月-19-101502-2024_Conflict.SLDASM

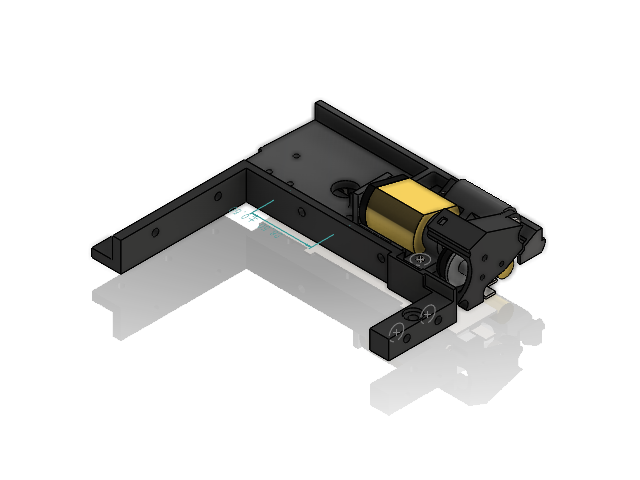
[picture p90: CAD file, 2025-02-23, last stored version]
结构/吐片机构/吐片机构_LAPTOP-NACPAVO6_7月-19-101502-2024_Conflict.SLDASM
吐片口机身钣金
吐片钣金连接件
MG825
吐片钣金固定销 x 2
马达座
1.6x14.6
1.6x20.6
齿轮A
齿轮B
齿轮C
齿轮D
齿轮E
齿轮罩
cross recessed cheese head screws type a gb x 5
hex thin nuts-grades ab-chamfered gb
吐片上巴
