ZeshuLiu/PolaMiya/结构Rev2/配件/Mamiya127镜头盖装配.SLDASM

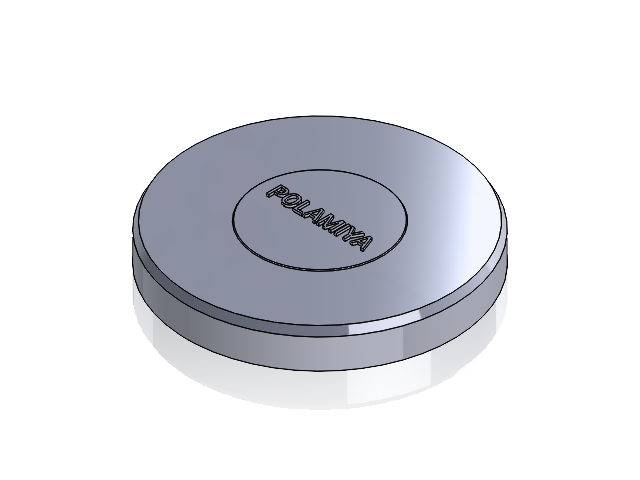
[picture p91: CAD file, 2025-02-23, last stored version]
结构Rev2/配件/Mamiya127镜头盖装配.SLDASM
Mamiya127镜头盖
Mamiya127铭牌
