ZeshuLiu/PolaMiya/结构Rev2N/全息取景器/瞄准装置.SLDASM

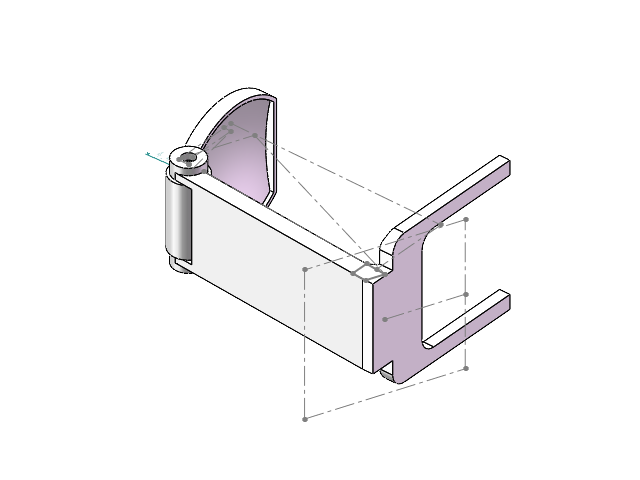
[picture p92: CAD file, 2026-03-20, last stored version]
结构Rev2N/全息取景器/瞄准装置.SLDASM
主座
镜座
反射镜片
