ZeshuLiu/PolaMiya/结构Rev2N/片仓总成/片仓总成.SLDASM

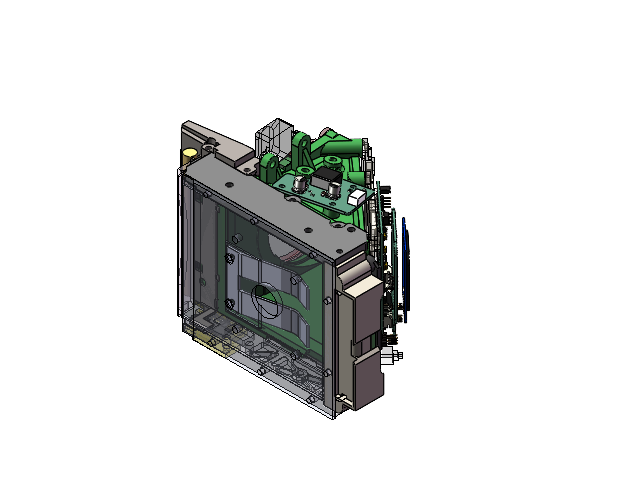
[picture p93: CAD file, 2026-03-20, last stored version]
结构Rev2N/片仓总成/片仓总成.SLDASM
主片仓
主反射镜
相纸盒
吐片口机身钣金-拆机
MG825-拆机
1.6x20.6-拆机
齿轮A-拆机
1.6x14.6-拆机
齿轮B-拆机
齿轮C-拆机
齿轮D-拆机
齿轮E-拆机
PinHeader_2x04_P1.27mm_Vertical.step x 2
R_0603_1608Metric.step x 42
C_0603_1608Metric.step x 30
SOT-23.step x 6
LQFP-64_10x10mm_P0.5mm.step
PinHeader_1x04_P2.00mm_Vertical.step
PinHeader_2x06_P1.27mm_Vertical.step
CP_EIA-3528-21_Kemet-B.step x 8
PinHeader_1x04_P2.54mm_Vertical.step x 3
LED_0805_2012Metric.step x 2
SOIC-8_3.9x4.9mm_P1.27mm.step x 2
SOT-23-6.step
JST_PH_S4B-PH-K_1x04_P2.00mm_Horizontal.step x 2
D_SMA.step x 3
SOT-563.step
Crystal_C26-LF_D2.1mm_L6.5mm_Horizontal.step x 3
SOT-223.step
PinSocket_1x02_P2.00mm_Vertical.step
L_APV_ANR5040.step
VSSOP-8_3x3mm_P0.65mm.step
TSSOP-14_4.4x5mm_P0.65mm.step
SOT-23-5.step
MFSOP6-4_4.4x3.6mm_P1.27mm.step
L_0805_2012Metric.step
PM_Controller_PCB.step
反光镜盖板
推片勾
MGN7导轨1
调焦桶盖
出片推杆
推片把手
齿轮盖
推片钩衬垫
电机卡环
齿轮维护盖
右侧板
18650电池
后侧板
电池负极弹片
电池正极弹片
激光测距SDM18
D_SOD_323.step x 2
CP_Elec_63x77.step x 2
C_1206_3216Metric-0.step x 2
R_0603_1608Metric-1.step x 4
LED_0805_2012Metric-2.step x 2
L_APV_APH1265-3.step
_autosave-MotroDrive_PCB.step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
