ZeshuLiu/PolaMiya/结构Rev2/片仓/片仓2.SLDASM

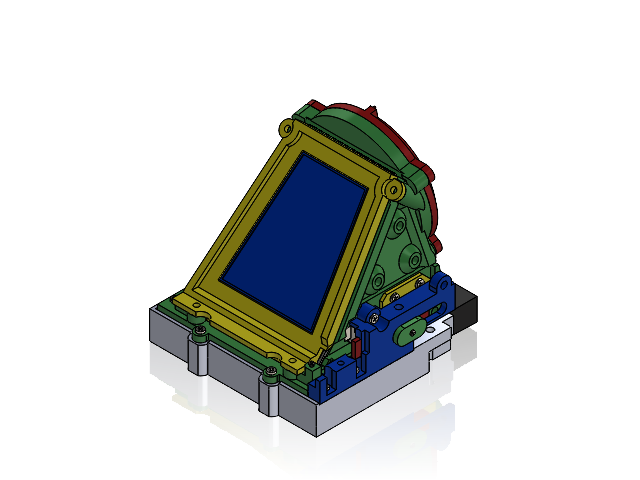
[picture p94: CAD file, 2025-02-23, last stored version]
结构Rev2/片仓/片仓2.SLDASM
相纸盒
片仓主框
片仓中框
cross recessed cheese head screws type a gb x 15
推片钩定位
出片推杆
推片勾
主反射镜
调焦桶盖
反射镜压板
反射镜压板盖
片仓侧杆
推片把手
